enny1170/ir-gateway/include/version.h

#ifndef VERSION_H
#define VERSION_H

/**************************************************************************************************************
 *  is defined in platformio.ini uncomment use this if you want to do it here
 * ***********************************************************************************************************/

// #define VERSION_MAJOR 2
// #define VERSION_MINOR 0
// #define VERSION_BUILD 3

// is defined in Platform.ini
// #define VERSION_STRING "2.0.3" 

#endif
